gteeger/PiScale/Raspberry Pi Code/kernel_space/mpu6050_motion_interrupt/mpu6050.h

#ifndef _MPU6050_H_
#define _MPU6050_H_

#define MOT_DUR 0x20

#define SELF_TEST_X 0x0D
#define SELF_TEST_Y 0x0E
#define SELF_TEST_Z 0x0F
#define SELF_TEST_A 0x10
#define SMPLRT_DIV 0x19
#define CONFIG 0x1A
#define GYRO_CONFIG 0x1B
#define ACCEL_CONFIG 0x1C
#define MOT_THR 0x1F
#define FIFO_EN 0x23
#define I2C_MST_CTRL 0x24
#define I2C_SLV0_ADDR 0x25
#define I2C_SLV0_REG 0x26
#define I2C_SLV0_CTRL 0x27
#define I2C_SLV1_ADDR 0x28
#define I2C_SLV1_REG 0x29
#define I2C_SLV1_CTRL 0x2A
#define I2C_SLV2_ADDR 0x2B
#define I2C_SLV2_REG 0x2C
#define I2C_SLV2_CTRL 0x2D
#define I2C_SLV3_ADDR 0x2E
#define I2C_SLV3_REG 0x2F
#define I2C_SLV3_CTRL 0x30
#define I2C_SLV4_ADDR 0x31
#define I2C_SLV4_REG 0x32
#define I2C_SLV4_DO 0x33
#define I2C_SLV4_CTRL 0x34
#define I2C_SLV4_DI 0x35
#define I2C_MST_STATUS 0x36
#define INT_PIN_CFG 0x37
#define INT_ENABLE 0x38
#define INT_STATUS 0x3A
#define ACCEL_XOUT_H 0x3B
#define ACCEL_XOUT_L 0x3C
#define ACCEL_YOUT_H 0x3D
#define ACCEL_YOUT_L 0x3E
#define ACCEL_ZOUT_H 0x3F
#define ACCEL_ZOUT_L 0x40
#define TEMP_OUT_H 0x41
#define TEMP_OUT_L 0x42
#define GYRO_XOUT_H 0x43
#define GYRO_XOUT_L 0x44
#define GYRO_YOUT_H 0x45
#define GYRO_YOUT_L 0x46
#define GYRO_ZOUT_H 0x47
#define GYRO_ZOUT_L 0x48
#define I2C_SLV0_DO 0x63
#define I2C_SLV1_DO 0x64
#define I2C_SLV2_DO 0x65
#define I2C_SLV3_DO 0x66
#define I2C_MST_DELAY_CTRL 0x67
//#define SIGNAL_PATH_RESET 0x68
#define MOT_DETECT_CTRL 0x69
#define USER_CTRL 0x6A
#define PWR_MGMT_1 0x6B
#define PWR_MGMT_2 0x6C
#define FIFO_COUNTH 0x72
#define FIFO_COUNTL 0x73
#define FIFO_R_W 0x74
#define WHO_AM_I 0x75
#define MPU6050_DEV_ADD 0x68
#define AFS_SEL 0x1C
#define FS_SEL 0x1B
#define TEMP_FIFO_EN_BIT 7
#define XG_FIFO_EN_BIT 6
#define YG_FIFO_EN_BIT 5
#define ZG_FIFO_EN_BIT 4
#define ACCEL_FIFO_EN_BIT 3
#define SLV2_FIFO_EN_BIT 2
#define SLV1_FIFO_EN_BIT 1
#define SLV0_FIFO_EN_BIT 0
#define DEV_RESET_BIT 7
#define FIFO_EN_BIT 6
#define FIFO_RESET_BIT 2


#endif /* _MPU6050_H_ */
